rzzzwilson/DigitalVFO/pyInstrument/discharge.png

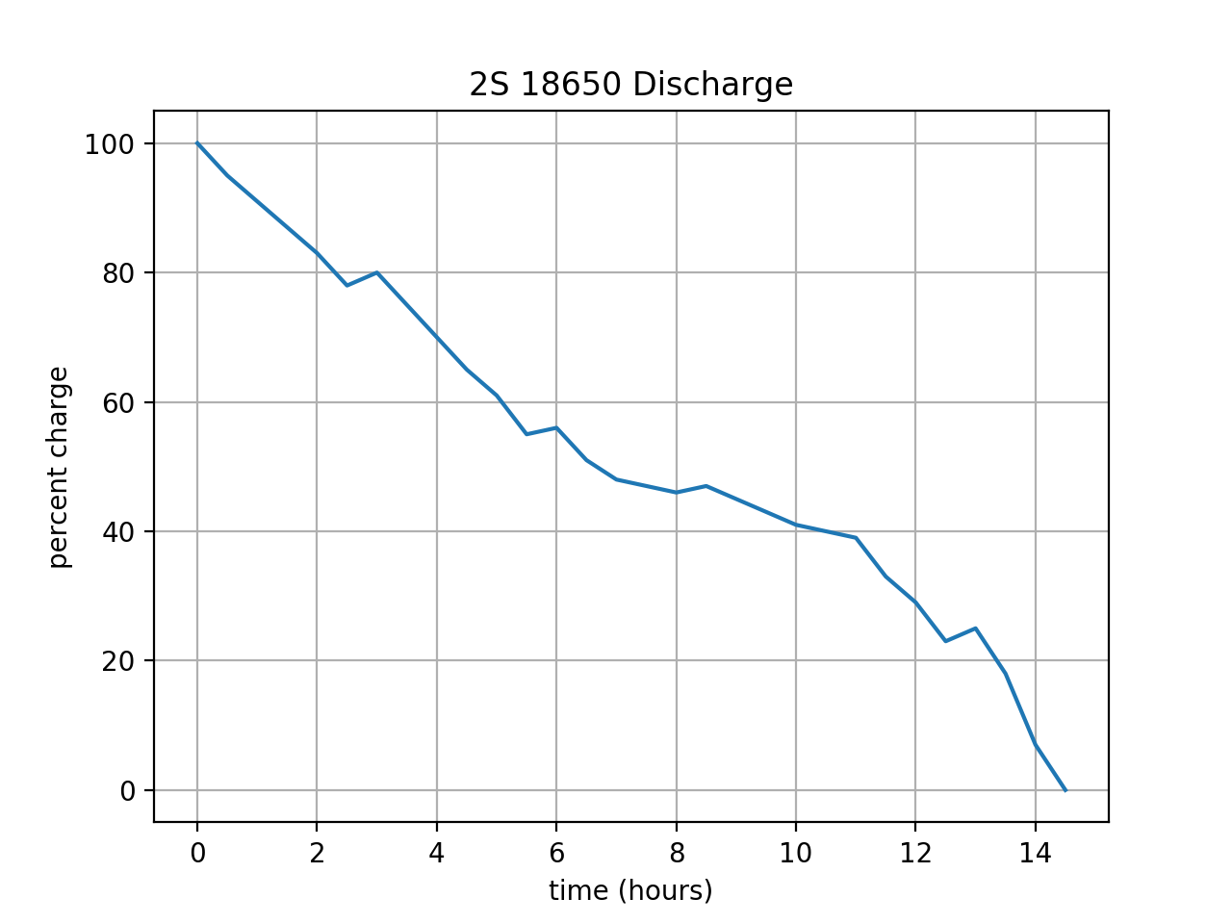
pyInstrument/discharge.png
